thingsforhackers/CopyMe84/hardware/pcb/etc/KiCad-Libraries/3D/SourceFiles/SMD_Passives/SMD-0805-scad.stl

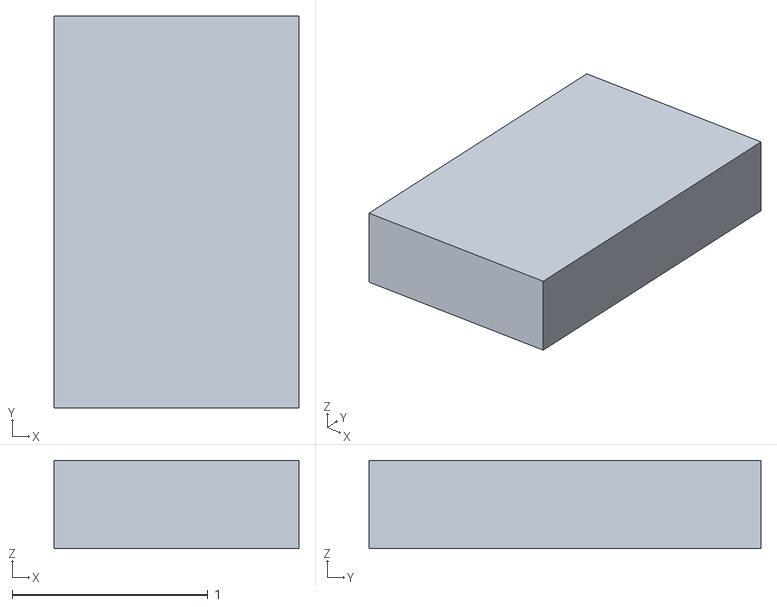
[picture p19: CAD file, 2017-01-17]
hardware/pcb/etc/KiCad-Libraries/3D/SourceFiles/SMD_Passives/SMD-0805-scad.stl
1.25 x 2.00 x 0.45
