thingsforhackers/CopyMe84/hardware/pcb/etc/KiCad-Libraries/3D/SourceFiles/SOIC/SOIC_08_4.0mm_5.0mm_1.27mm-wings.stl

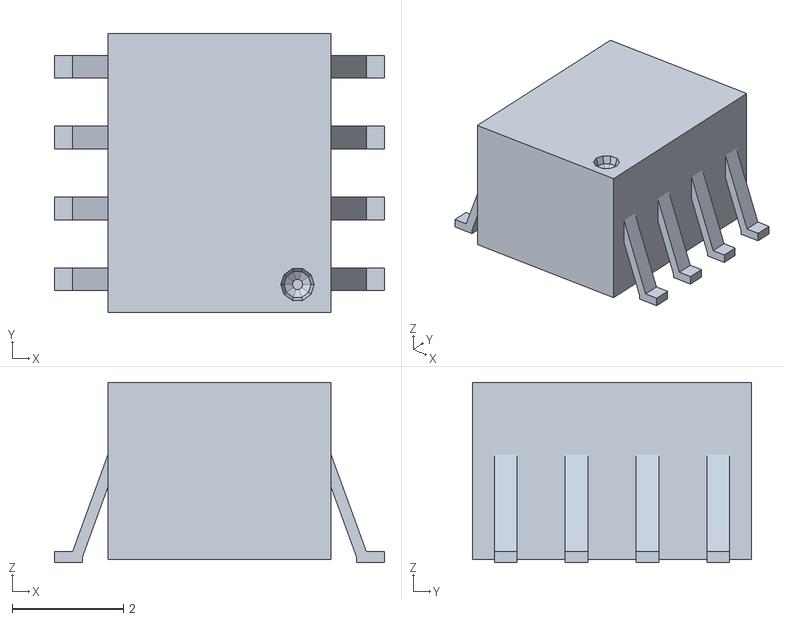
[picture p20: CAD file, 2017-01-17]
hardware/pcb/etc/KiCad-Libraries/3D/SourceFiles/SOIC/SOIC_08_4.0mm_5.0mm_1.27mm-wings.stl
5.92 x 5.00 x 3.23
