thingsforhackers/CopyMe84/hardware/pcb/etc/KiCad-Libraries/3D/SourceFiles/SolarCells/Spectrolab_TASC1-SCAD.stl

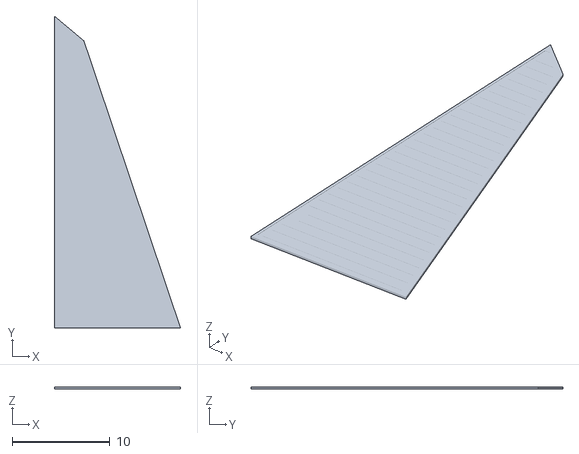
[picture p21: CAD file, 2017-01-17]
hardware/pcb/etc/KiCad-Libraries/3D/SourceFiles/SolarCells/Spectrolab_TASC1-SCAD.stl
12.9 x 31.9 x 0.178
