thingsforhackers/CopyMe84/hardware/pcb/etc/KiCad-Libraries/3D/SourceFiles/SON-10/SON-10-wings.stl

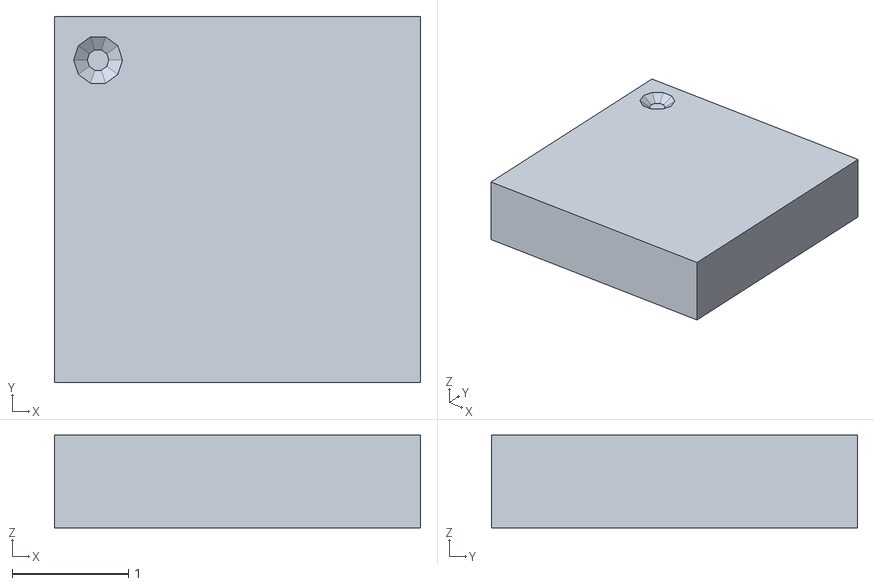
[picture p22: CAD file, 2017-01-17]
hardware/pcb/etc/KiCad-Libraries/3D/SourceFiles/SON-10/SON-10-wings.stl
3.15 x 3.15 x 0.8
