thingsforhackers/CopyMe84/hardware/pcb/etc/KiCad-Libraries/3D/SourceFiles/SOT-23/SOT-23-6-wings.stl

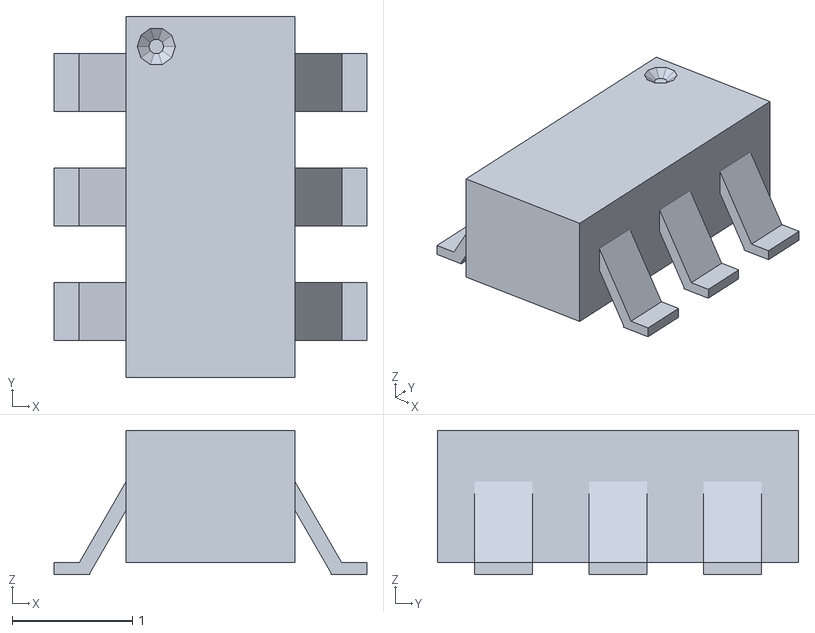
[picture p23: CAD file, 2017-01-17]
hardware/pcb/etc/KiCad-Libraries/3D/SourceFiles/SOT-23/SOT-23-6-wings.stl
2.60 x 3.00 x 1.20
