thingsforhackers/CopyMe84/hardware/pcb/etc/KiCad-Libraries/3D/SourceFiles/SOT-363/SOT-363-Wings.stl

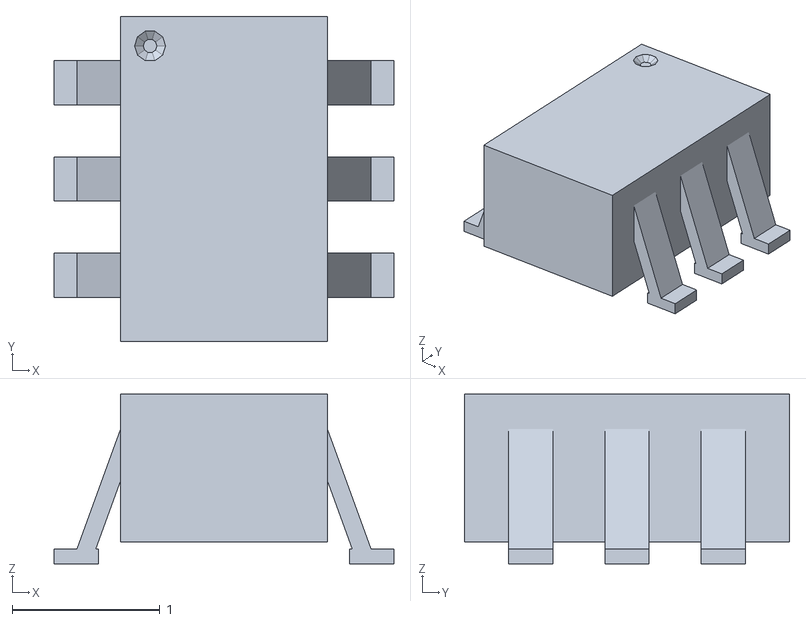
[picture p24: CAD file, 2017-01-17]
hardware/pcb/etc/KiCad-Libraries/3D/SourceFiles/SOT-363/SOT-363-Wings.stl
2.30 x 2.20 x 1.15
