thingsforhackers/CopyMe84/hardware/pcb/etc/KiCad-Libraries/3D/SourceFiles/SSOP/SSOP_08_3.0mm_3.0mm_0.65mm-scad.stl

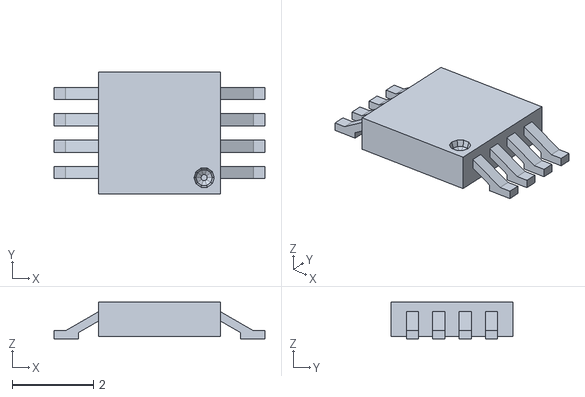
[picture p25: CAD file, 2017-01-17]
hardware/pcb/etc/KiCad-Libraries/3D/SourceFiles/SSOP/SSOP_08_3.0mm_3.0mm_0.65mm-scad.stl
5.20 x 3.00 x 0.9
