thingsforhackers/CopyMe84/hardware/pcb/etc/KiCad-Libraries/3D/SourceFiles/Switches/Switch-Eswitch-Slide-Wings.stl

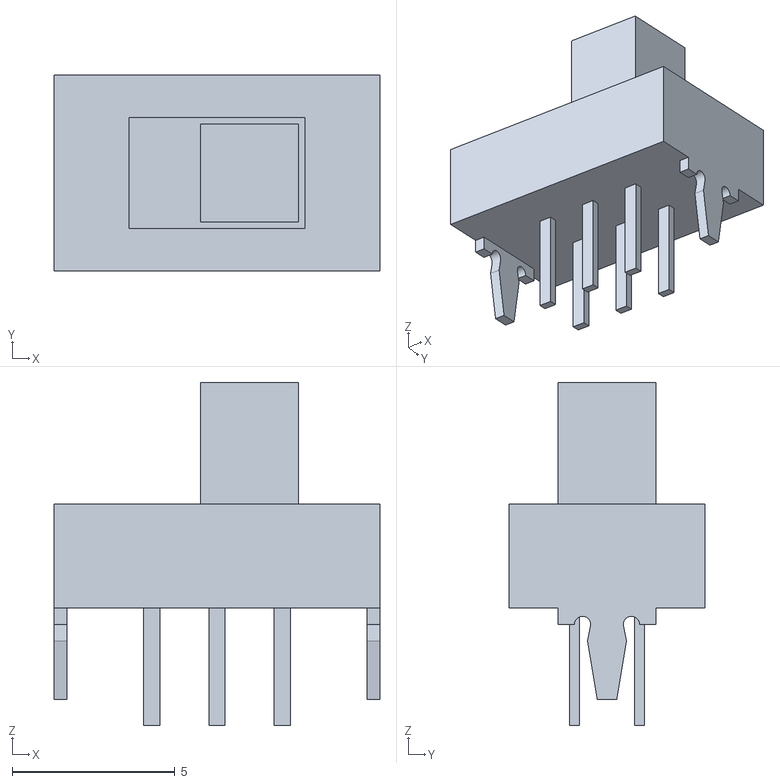
[picture p26: CAD file, 2017-01-17]
hardware/pcb/etc/KiCad-Libraries/3D/SourceFiles/Switches/Switch-Eswitch-Slide-Wings.stl
10.0 x 6.00 x 10.5
