thingsforhackers/CopyMe84/hardware/pcb/etc/KiCad-Libraries/3D/SourceFiles/Venus638/Venus638-SCAD.stl

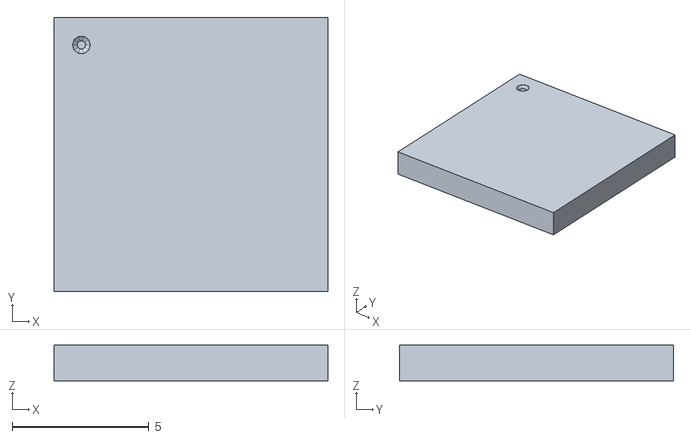
[picture p27: CAD file, 2017-01-17]
hardware/pcb/etc/KiCad-Libraries/3D/SourceFiles/Venus638/Venus638-SCAD.stl
10.0 x 10.0 x 1.30
