thingsforhackers/CopyMe84/hardware/pcb/etc/KiCad-Libraries/3D/SourceFiles/Connectors/CONN_1x6/CONN_1x6_Male.stl

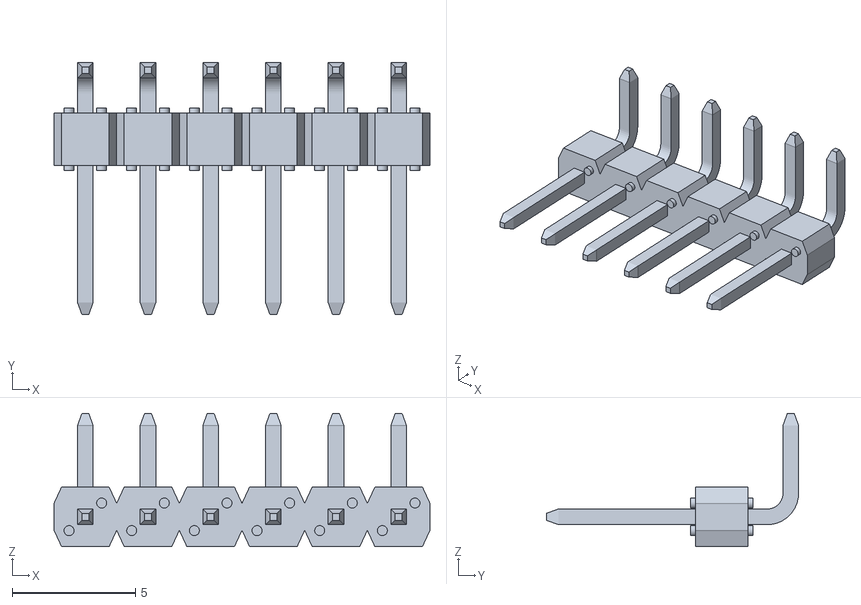
[picture p28: CAD file, 2017-01-17]
hardware/pcb/etc/KiCad-Libraries/3D/SourceFiles/Connectors/CONN_1x6/CONN_1x6_Male.stl
15.2 x 10.2 x 5.40
