thingsforhackers/CopyMe84/hardware/pcb/etc/KiCad-Libraries/3D/SourceFiles/Connectors/CONN_2x6/CONN_2x6_Male.stl

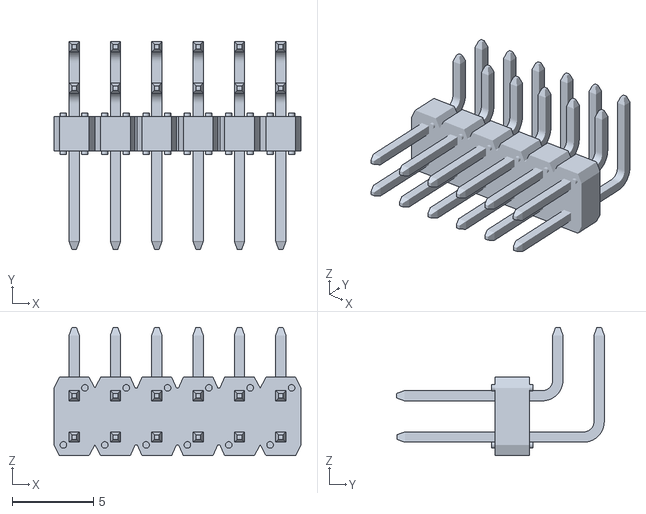
[picture p29: CAD file, 2017-01-17]
hardware/pcb/etc/KiCad-Libraries/3D/SourceFiles/Connectors/CONN_2x6/CONN_2x6_Male.stl
15.2 x 12.8 x 7.89
