thingsforhackers/CopyMe84/hardware/pcb/etc/KiCad-Libraries/3D/SourceFiles/SD_Objects/SD-Amp-microSlot-SCAD.stl

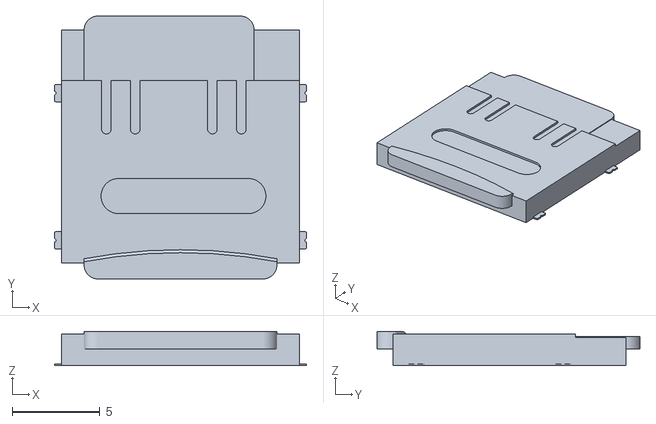
[picture p30: CAD file, 2017-01-17]
hardware/pcb/etc/KiCad-Libraries/3D/SourceFiles/SD_Objects/SD-Amp-microSlot-SCAD.stl
14.4 x 15.0 x 1.95
