thingsforhackers/CopyMe84/hardware/pcb/etc/KiCad-Libraries/3D/SourceFiles/SMD_Passives/SMD-2010-scad.stl

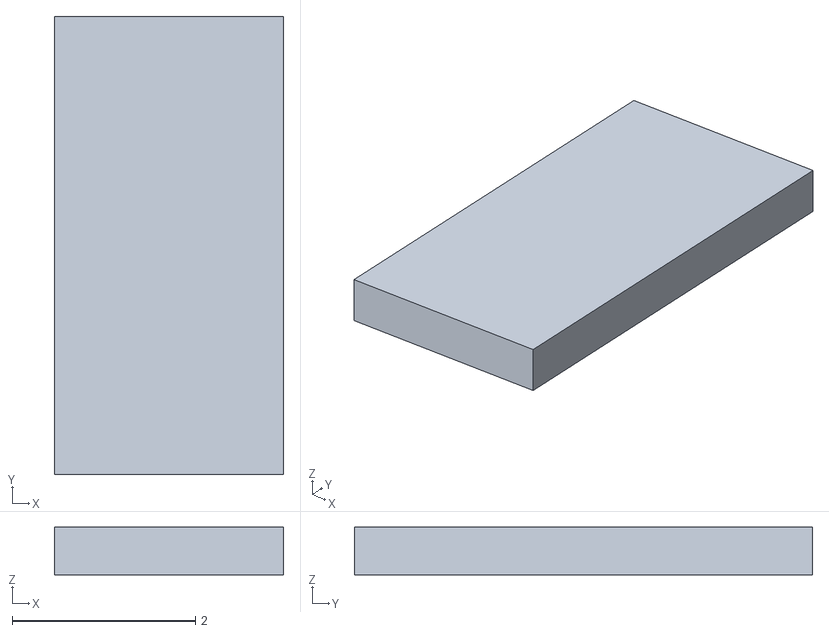
[picture p31: CAD file, 2017-01-17]
hardware/pcb/etc/KiCad-Libraries/3D/SourceFiles/SMD_Passives/SMD-2010-scad.stl
2.50 x 5.00 x 0.52
