thingsforhackers/CopyMe84/hardware/pcb/etc/KiCad-Libraries/3D/SourceFiles/SolarCells/Spectrolab_CIC-Wings.stl.stl

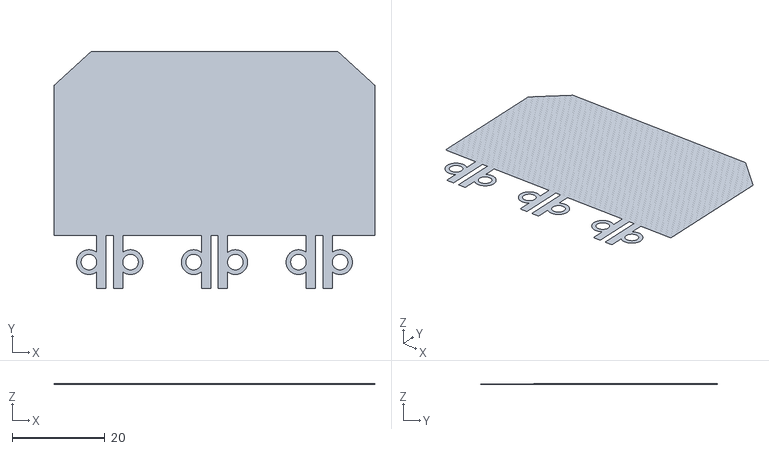
[picture p32: CAD file, 2017-01-17]
hardware/pcb/etc/KiCad-Libraries/3D/SourceFiles/SolarCells/Spectrolab_CIC-Wings.stl.stl
69.1 x 51.1 x 0.178
