thingsforhackers/CopyMe84/hardware/pcb/etc/KiCad-Libraries/3D/SourceFiles/SON-10/SON-10-scad.stl

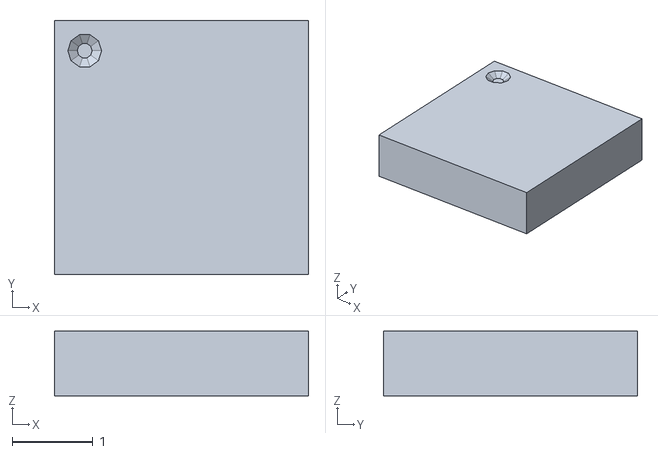
[picture p33: CAD file, 2017-01-17]
hardware/pcb/etc/KiCad-Libraries/3D/SourceFiles/SON-10/SON-10-scad.stl
3.15 x 3.15 x 0.8
