thingsforhackers/CopyMe84/hardware/pcb/etc/KiCad-Libraries/3D/SourceFiles/SSOP/SSOP_20_4.5mm_6.6mm_0.65mm-scad.stl

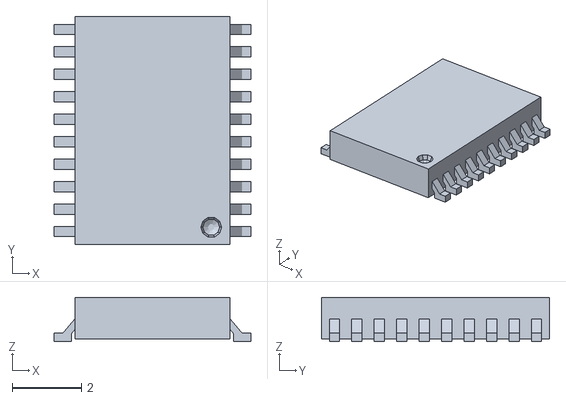
[picture p34: CAD file, 2017-01-17]
hardware/pcb/etc/KiCad-Libraries/3D/SourceFiles/SSOP/SSOP_20_4.5mm_6.6mm_0.65mm-scad.stl
5.70 x 6.60 x 1.27
