thingsforhackers/CopyMe84/hardware/pcb/etc/KiCad-Libraries/3D/SourceFiles/Switches/Switch-DIP-SMD-3-SCAD.stl

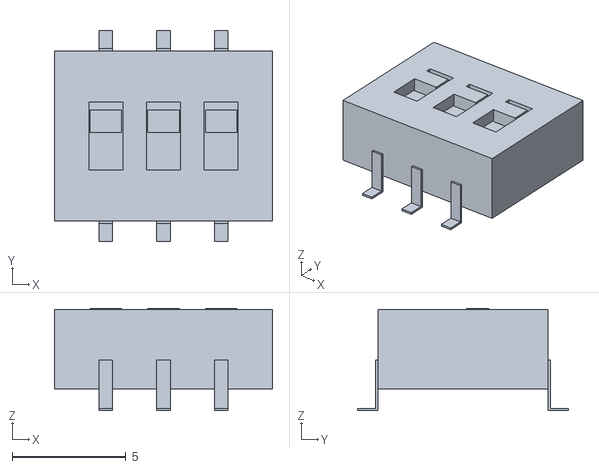
[picture p35: CAD file, 2017-01-17]
hardware/pcb/etc/KiCad-Libraries/3D/SourceFiles/Switches/Switch-DIP-SMD-3-SCAD.stl
9.60 x 9.30 x 4.50
