thingsforhackers/CopyMe84/hardware/pcb/etc/KiCad-Libraries/3D/SourceFiles/Connectors/Deans/Deans-SCAD.stl

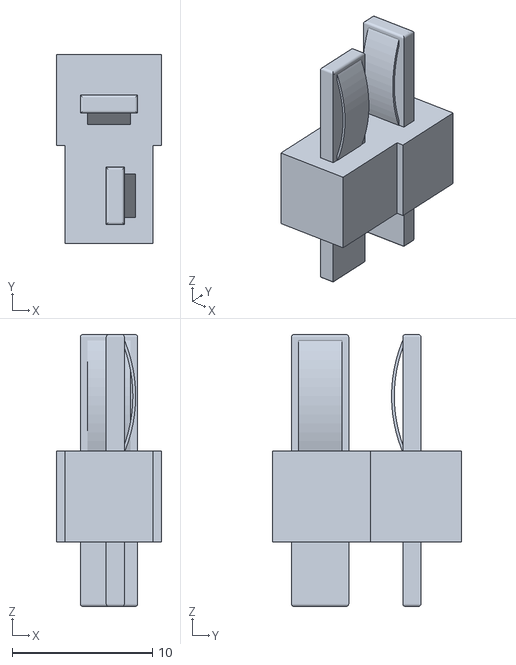
[picture p36: CAD file, 2017-01-17]
hardware/pcb/etc/KiCad-Libraries/3D/SourceFiles/Connectors/Deans/Deans-SCAD.stl
7.50 x 13.5 x 19.4
