thingsforhackers/CopyMe84/hardware/pcb/etc/KiCad-Libraries/3D/SourceFiles/SOIC/SOIC_08_4.0mm_5.8mm_1.27mm-scad.stl

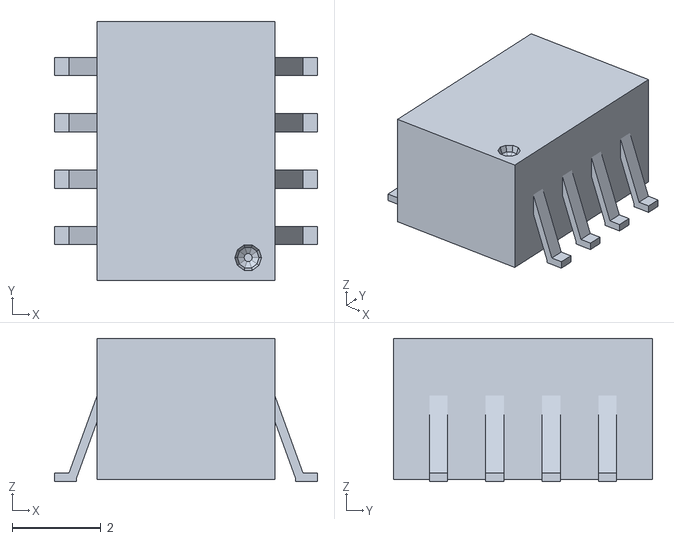
[picture p37: CAD file, 2017-01-17]
hardware/pcb/etc/KiCad-Libraries/3D/SourceFiles/SOIC/SOIC_08_4.0mm_5.8mm_1.27mm-scad.stl
5.92 x 5.84 x 3.23
