thingsforhackers/CopyMe84/hardware/pcb/etc/KiCad-Libraries/3D/SourceFiles/Switches/Switch-TE-Slide-SCAD.stl

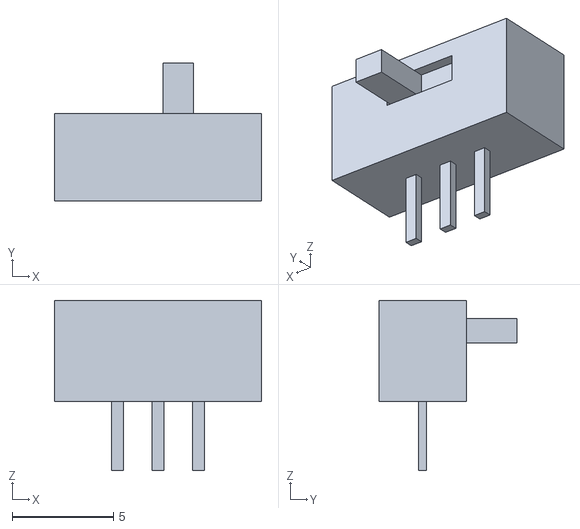
[picture p38: CAD file, 2017-01-17]
hardware/pcb/etc/KiCad-Libraries/3D/SourceFiles/Switches/Switch-TE-Slide-SCAD.stl
10.2 x 6.80 x 8.40
