thingsforhackers/CopyMe84/hardware/pcb/etc/KiCad-Libraries/3D/SourceFiles/SMD_Passives/SMD-1206-scad.stl

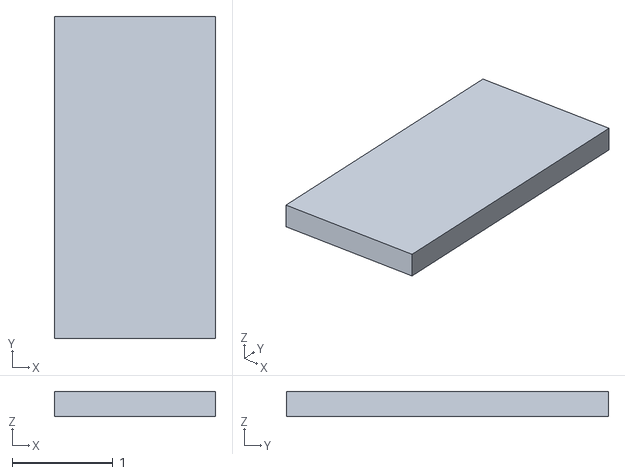
[picture p39: CAD file, 2017-01-17]
hardware/pcb/etc/KiCad-Libraries/3D/SourceFiles/SMD_Passives/SMD-1206-scad.stl
1.60 x 3.20 x 0.25
