thingsforhackers/CopyMe84/button.c

/*
 * button.c
 *
 *  Created on: 5 Jun 2016
 *      Author: njohn
 */
#include <avr/io.h>
#include "button.h"
#include "tmr.h"


static const uint32_t DEBOUNCE_TIME = 50; //ms
static const uint32_t HOLD_TIME = 2000; //ms

void initButtons(ButtonCtx* ctx, uint8_t count)
{
  for( uint8_t idx = 0; idx < count; idx++)
  {
    ctx[idx].state = BUTTON_UP;
  }
}

void updateButtons(ButtonCtx* buttons, uint8_t count)
{
  for( uint8_t idx = 0; idx < count; idx++)
  {
    ButtonCtx* button = &buttons[idx];
    const uint8_t pressed = *button->portAddr & _BV(button->bitMask) ? 0 : 1;
    switch(button->state)
    {
      case BUTTON_UP:
      {
        if(pressed)
        {
          button->time = millis();
          button->state = BUTTON_PRESSED;
        }
        break;
      }

      case BUTTON_PRESSED:
      {
        button->state = BUTTON_DEBOUCE;
        break;
      }

      case BUTTON_DEBOUCE:
      {
          if( (millis() - button->time) > DEBOUNCE_TIME )
          {
              if(pressed)
              {
                  button->time = millis();
                  button->state = BUTTON_DOWN;
              }
              else
              {
                  button->state = BUTTON_UP;
              }
          }
          break;
      }

      case BUTTON_DOWN:
      {
          if(pressed)
          {
              if( (millis() - button->time) > HOLD_TIME )
              {
                  button->state = BUTTON_HELD;
              }
          }
          else
          {
              button->state = BUTTON_RELEASED;
          }
          break;
      }

      case BUTTON_HELD:
      {
          if(!pressed)
          {
              button->state = BUTTON_UP;
          }
          break;
      }

      case BUTTON_RELEASED:
      {
          button->state = BUTTON_UP;
          break;
      }
    }
  }
}
