thingsforhackers/CopyMe84/tune.h

/*
 * tune.h
 *
 *  Created on: 11 Jun 2016
 *      Author: njohn
 */

#ifndef TUNE_H_
#define TUNE_H_

#define TUNE_LENGTH 544 // length of array
#define TUNE2_LENGTH 8 // length of array

extern const uint16_t noteArray[];
extern const uint16_t noteArray2[];

#endif /* TUNE_H_ */
